geerlingguy/equip-1/design/firehat/firehat.kicad_sch

## KiCad design design/firehat/firehat.kicad_sch (2026-03-26)

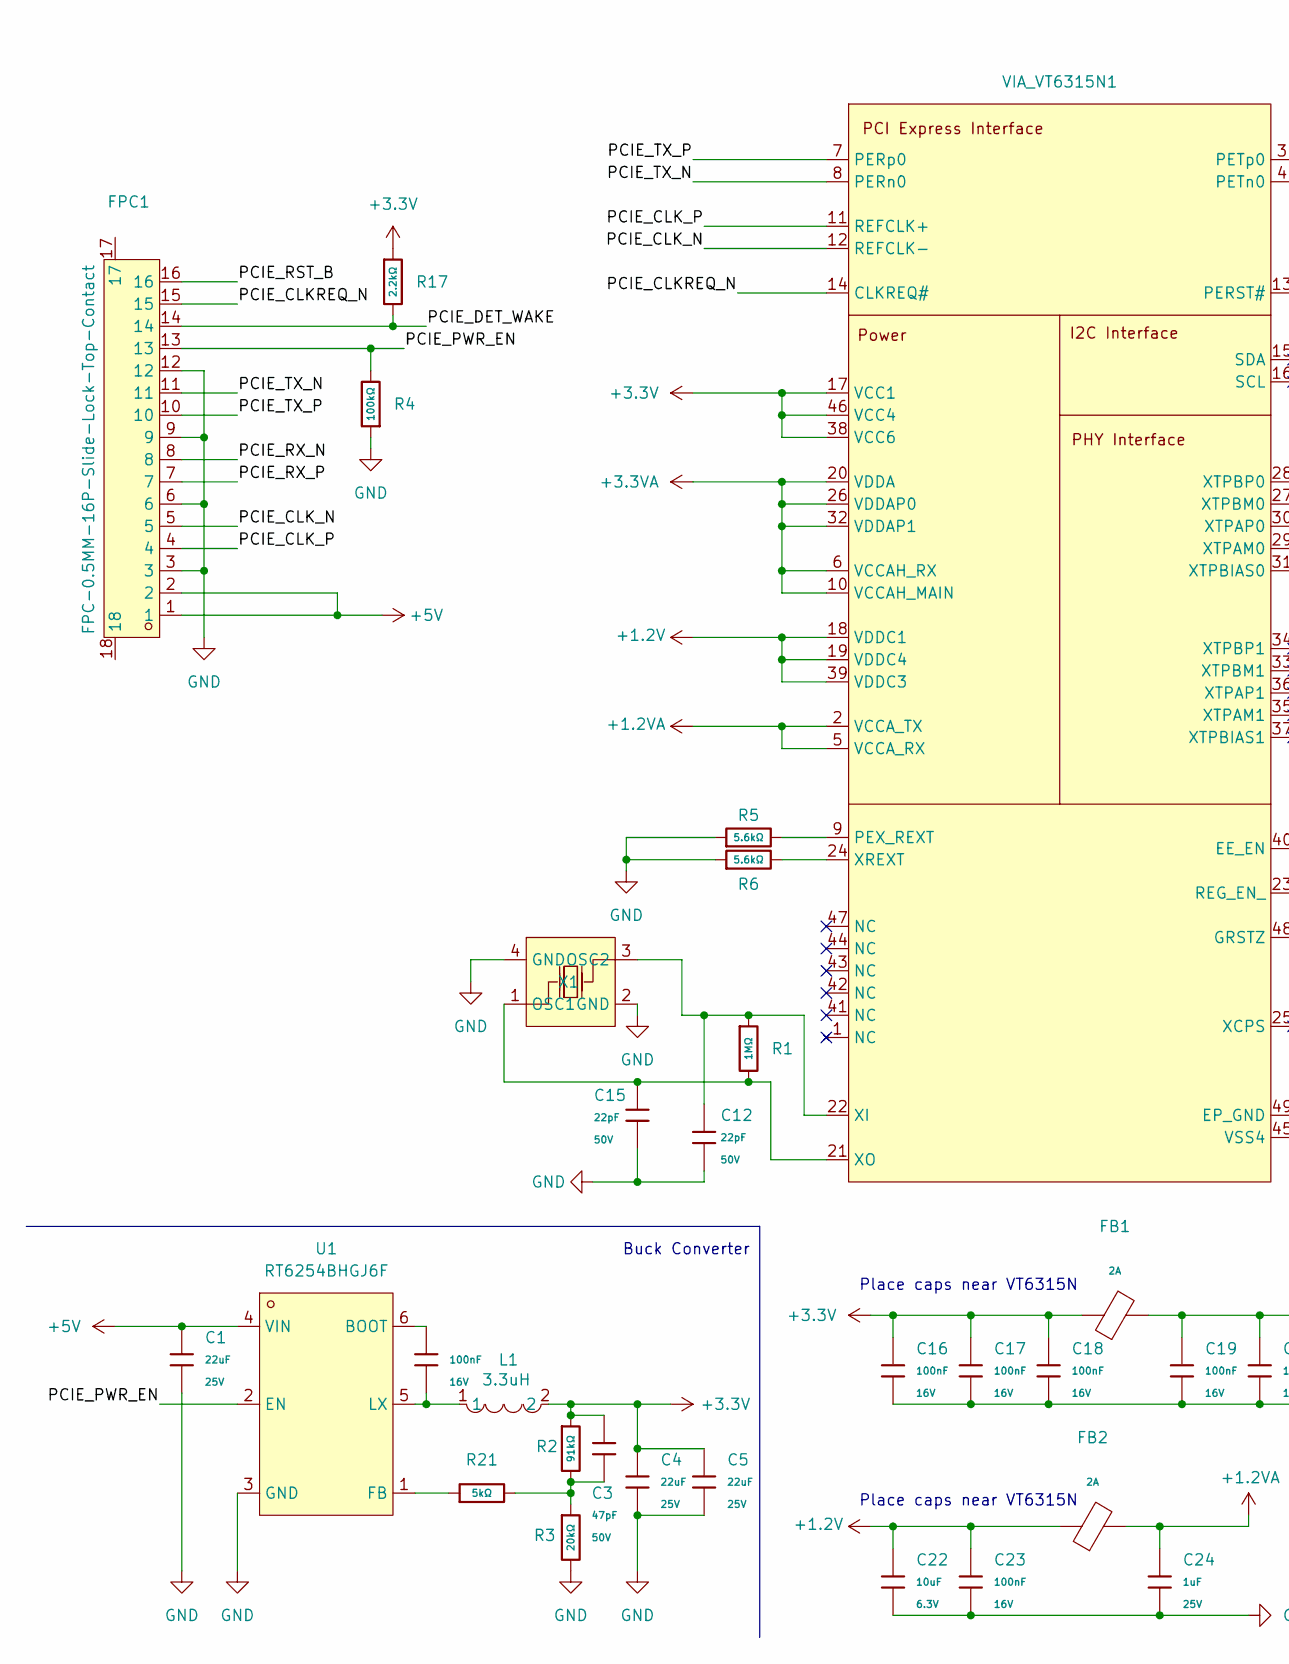
[picture p3: schematic firehat.kicad_sch, part in row 1, column 1]

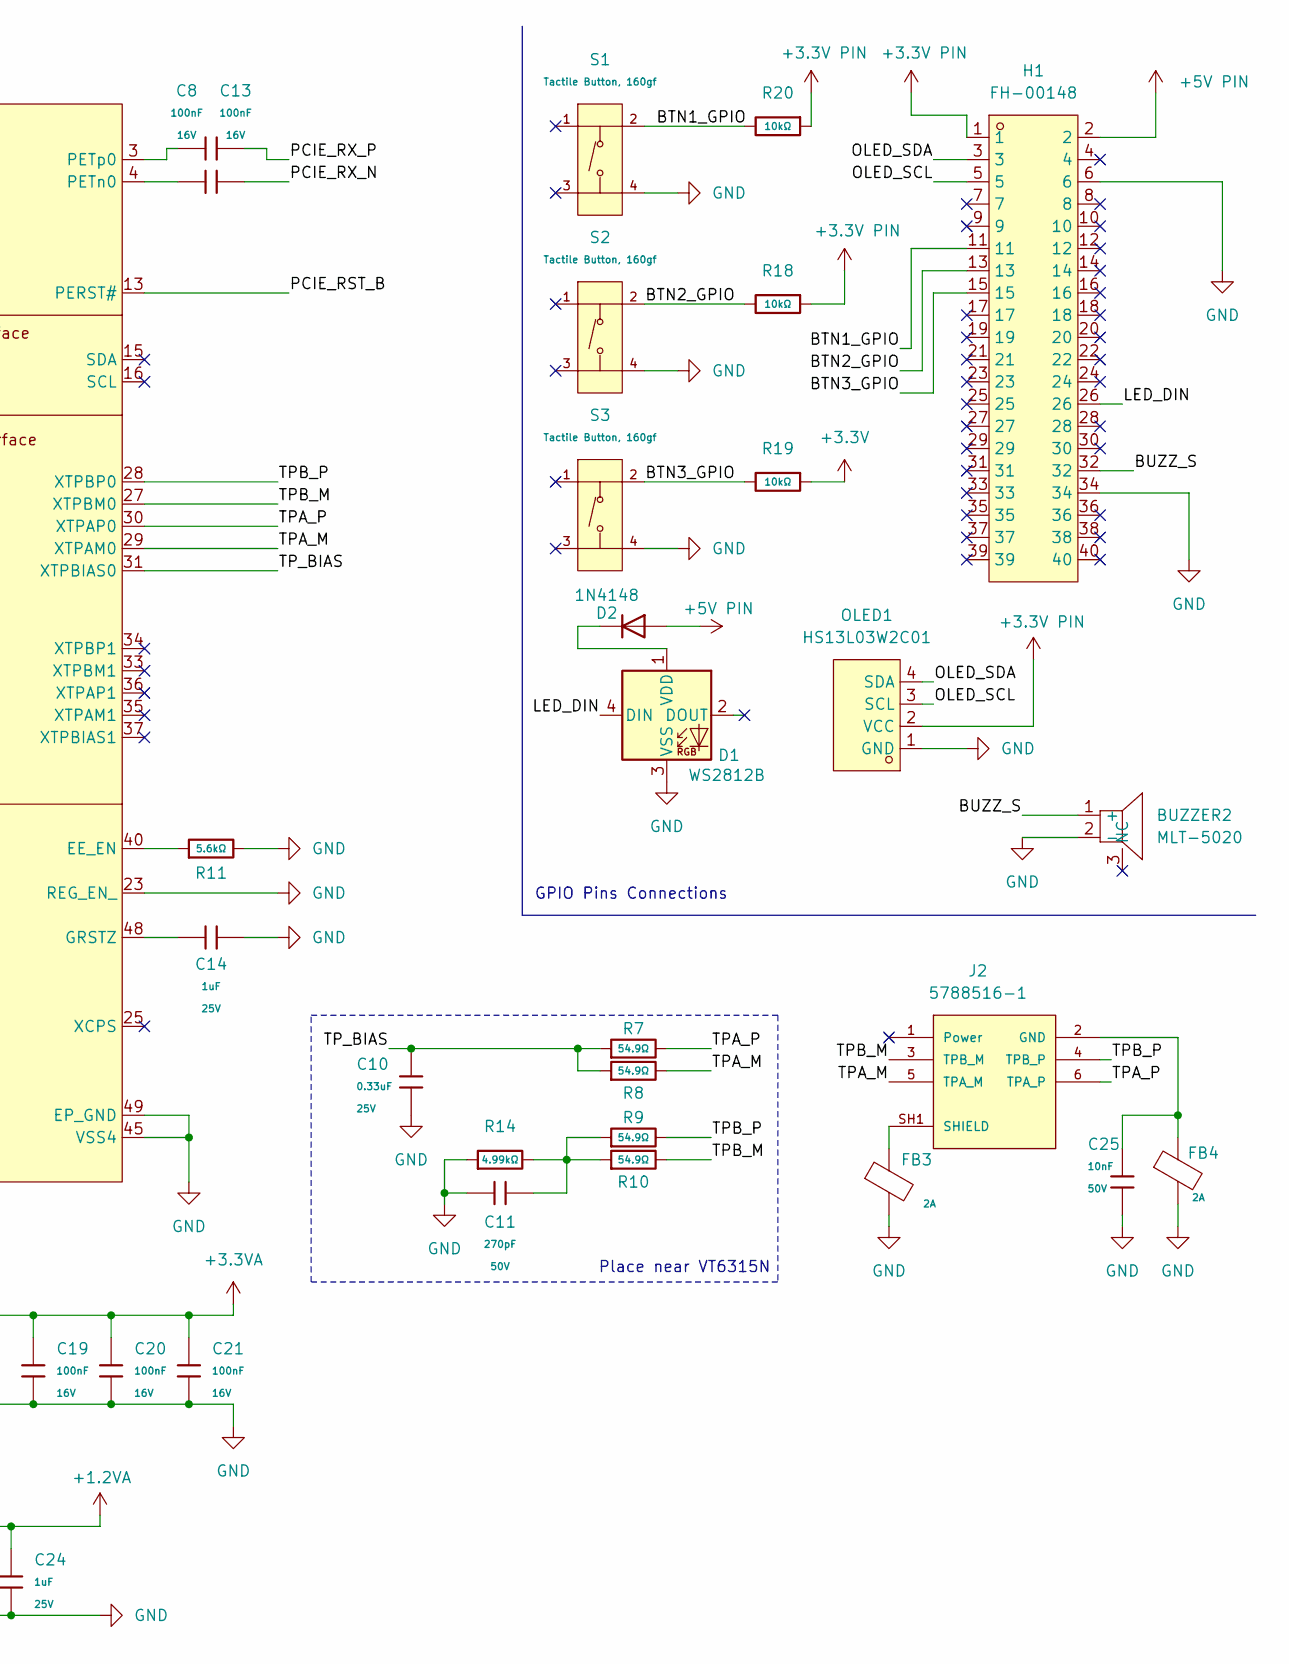
[picture p4: schematic firehat.kicad_sch, part in row 1, column 2]

Parts:
BUZZER2: MLT-5020; BUZ-SMD_L5.0-W5.5-P4.60; LCSC Part C94598
C1, C4, C5: 22uF; C_0805; Voltage Rated 25V; Tolerance ±20%; Part CL21A226MAQNNNE; LCSC C45783
C2, C8, C13, C16, C17, C18, C19, C20, C21, C23: 100nF; C_0402; Voltage Rated 16V; Tolerance ±10%; Part CL05B104KO5NNNC; LCSC C1525
C3: 47pF; C_0402; Voltage Rated 50V; Tolerance ±5%; Part 0402CG470J500NT; LCSC C1567
C10: 0.33uF; C_0402; Voltage Rated 25V; Tolerance ±10%; Part CL05A105KA5NQNC; LCSC C52923
C11: 270pF; C_0402; Voltage Rated 50V; Tolerance ±10%; Part 0402B221K500NT; LCSC C1530
C12, C15: 22pF; C_0402; Voltage Rated 50V; Tolerance ±5%; Part 0402CG220J500NT; LCSC C1555
C14, C24: 1uF; C_0402; Voltage Rated 25V; Tolerance ±10%; Part CL05A105KA5NQNC; LCSC C52923
C22: 10uF; C_0402; Voltage Rated 6.3V; Tolerance ±20%; Part CL05A106MQ5NUNC; LCSC C15525
C25: 10nF; C_0402; Voltage Rated 50V; Tolerance ±10%; Part CL05B103KB5NNNC; LCSC C15195
D1: WS2812B; LED_WS2812B_PLCC4_5.0x5.0mm_P3.2mm; LCSC C22461793
D2: 1N4148; SOD-123_L2.8-W1.8-LS3.7-RD
FB1, FB2, FB3, FB4: FB_0603; Current Rating 2A; Tolerance ±25%; Part BLM18PG121SN1D; LCSC C14709
FPC1: FPC-0.5MM-16P-Slide-Lock-Top-Contact; FPC-SMD_16P-P0.50_AFC07-S16ECC-00; LCSC Part C11088
H1: FH-00148; HDR-TH_40P-P2.54-V-F-R2-C20-S2.54; LCSC Part C132132
J2: 5788516-1; TE_5788516-1; PARTREV A
L1: 3.3uH; IND-SMD_L4.4-W4.2; LCSC Part C167205
OLED1: HS13L03W2C01; OLED-TH_L35.4-W33.5_HS13L03W2C01; LCSC Part C7465997
R1: 1MΩ; R_0402; Overload Voltage (Max) 50V; Tolerance ±1%; Part 0402WGF1004TCE; LCSC C26083
R2: 91kΩ; R_0603; Overload Voltage (Max) 75V; Tolerance ±1%; Part 0603WAF9102T5E; LCSC C23265
R3: 20kΩ; R_0603; Overload Voltage (Max) 75V; Tolerance ±1%; Part 0603WAF2002T5E; LCSC C4184
R4: 100kΩ; R_0402; Overload Voltage (Max) 50V; Tolerance ±1%; Part 0402WGF1003TCE; LCSC C25741
R5, R6, R11: 5.6kΩ; R_0402; Overload Voltage (Max) 50V; Tolerance ±1%; Part 0402WGF5601TCE; LCSC C25908
R7, R8, R9, R10: 54.9Ω; R_0402; Overload Voltage (Max) 50V; Tolerance ±1%; Part 0402WGF510JTCE; LCSC C25125
R14: 4.99kΩ; R_0402; Overload Voltage (Max) 50V; Tolerance ±1%; Part 0402WGF4701TCE; LCSC C25900
R17: 2.2kΩ; R_0402; Overload Voltage (Max) 50V; Tolerance ±1%; Part 0402WGF2201TCE; LCSC C25879
R18, R19, R20: 10kΩ; R_0402; Overload Voltage (Max) 50V; Tolerance ±1%; Part 0402WGF1002TCE; LCSC C25744
R21: 5kΩ; R_0402; Overload Voltage (Max) 50V; Tolerance ±1%; Part 0402WGF5101TCE; LCSC C25905
S1, S2, S3: Tactile Button, 160gf; SW-SMD_4P-L5.1-W5.1-P3.70-LS6.5-TL-2; Voltage Rating (Dc) 12V; Part TS-1187A-B-A-B; LCSC C318884
U1: RT6254BHGJ6F; TSOT-23-6_L2.9-W1.6-P0.95-LS2.8-BR; LCSC Part C3194280
VIA_VT6315N1: Infineon_MLPQ-48-1EP_7x7mm_P0.5mm_EP5.15x5.15mm
X1: X322524576MOB4SC; CRYSTAL-SMD_4P-L3.2-W2.5-BL; LCSC Part C70568

Connections:
+1.2V: C22.1, C23.1, FB2.1, VIA_VT6315N1.18 (VDDC1), VIA_VT6315N1.19 (VDDC4), VIA_VT6315N1.39 (VDDC3)
+1.2VA: C24.1, FB2.2, VIA_VT6315N1.2 (VCCA_TX), VIA_VT6315N1.5 (VCCA_RX)
+3.3V: C3.1, C4.1, C5.1, C16.1, C17.1, C18.1, FB1.1, L1.2, R2.1, R17.1, R19.1, VIA_VT6315N1.17 (VCC1), VIA_VT6315N1.38 (VCC6), VIA_VT6315N1.46 (VCC4)
+3.3V PIN: H1.1, OLED1.2 (VCC), R18.1, R20.1
+3.3VA: C19.1, C20.1, C21.1, FB1.2, VIA_VT6315N1.6 (VCCAH_RX), VIA_VT6315N1.10 (VCCAH_MAIN), VIA_VT6315N1.20 (VDDA), VIA_VT6315N1.26 (VDDAP0), VIA_VT6315N1.32 (VDDAP1)
+5V: C1.1, FPC1.1, FPC1.2, U1.4 (VIN)
+5V PIN: D2.2 (A), H1.2
BTN1_GPIO: H1.11, R20.2, S1.2 (B)
BTN2_GPIO: H1.13, R18.2, S2.2 (B)
BTN3_GPIO: H1.15, R19.2, S3.2 (B)
BUZZ_S: BUZZER2.1 (+), H1.32
GND: BUZZER2.2 (-), C1.2, C4.2, C5.2, C10.2, C11.1, C12.2, C14.1, C15.2, C16.2, C17.2, C18.2, C19.2, C20.2, C21.2, C22.2, C23.2, C24.2, C25.2, D1.3 (VSS), FB3.2, FB4.2, FPC1.3, FPC1.6, FPC1.9, FPC1.12, H1.6, H1.34, OLED1.1 (GND), R3.2, R4.1, R5.1, R6.1, R11.2, R14.1, S1.4 (D), S2.4 (D), S3.4 (D), U1.3 (GND), VIA_VT6315N1.23 (REG_EN_), VIA_VT6315N1.45 (VSS4), VIA_VT6315N1.49 (EP_GND), X1.2 (GND), X1.4 (GND)
LED_DIN: D1.4 (DIN), H1.26
unnamed: C2.1, U1.6 (BOOT)
unnamed: C2.2, L1.1, U1.5 (LX)
unnamed: C3.2, R2.2, R3.1, R21.2
unnamed: C8.2, VIA_VT6315N1.3 (PETp0)
unnamed: C11.2, R9.1, R10.1, R14.2
unnamed: C12.1, R1.1, VIA_VT6315N1.22 (XI), X1.3 (OSC2)
unnamed: C13.2, VIA_VT6315N1.4 (PETn0)
unnamed: C14.2, VIA_VT6315N1.48 (GRSTZ)
unnamed: C15.1, R1.2, VIA_VT6315N1.21 (XO), X1.1 (OSC1)
unnamed: C25.1, FB4.1, J2.2 (GND)
unnamed: D1.1 (VDD), D2.1 (K)
unnamed: FB3.1, J2.SH1 (SHIELD), J2.SH2 (SHIELD), J2.SH3 (SHIELD), J2.SH4 (SHIELD)
unnamed: R5.2, VIA_VT6315N1.9 (PEX_REXT)
unnamed: R6.2, VIA_VT6315N1.24 (XREXT)
unnamed: R11.1, VIA_VT6315N1.40 (EE_EN)
unnamed: R21.1, U1.1 (FB)
OLED_SCL: H1.5, OLED1.3 (SCL)
OLED_SDA: H1.3, OLED1.4 (SDA)
PCIE_CLKREQ_N: FPC1.15, VIA_VT6315N1.14 (CLKREQ#)
PCIE_CLK_N: FPC1.5, VIA_VT6315N1.12 (REFCLK-)
PCIE_CLK_P: FPC1.4, VIA_VT6315N1.11 (REFCLK+)
PCIE_DET_WAKE: FPC1.14, R17.2
PCIE_PWR_EN: FPC1.13, R4.2, U1.2 (EN)
PCIE_RST_B: FPC1.16, VIA_VT6315N1.13 (PERST#)
PCIE_RX_N: C13.1, FPC1.8
PCIE_RX_P: C8.1, FPC1.7
PCIE_TX_N: FPC1.11, VIA_VT6315N1.8 (PERn0)
PCIE_TX_P: FPC1.10, VIA_VT6315N1.7 (PERp0)
TPA_M: J2.5 (TPA_M), R8.2, VIA_VT6315N1.29 (XTPAM0)
TPA_P: J2.6 (TPA_P), R7.2, VIA_VT6315N1.30 (XTPAP0)
TPB_M: J2.3 (TPB_M), R10.2, VIA_VT6315N1.27 (XTPBM0)
TPB_P: J2.4 (TPB_P), R9.2, VIA_VT6315N1.28 (XTPBP0)
TP_BIAS: C10.1, R7.1, R8.1, VIA_VT6315N1.31 (XTPBIAS0)

Notes on the sheet:
Place caps near VT6315N
Buck Converter
Place near VT6315N
GPIO Pins Connections
